IteraThor/IT2-Documentation/images/05_baseplate/01_front_back.png

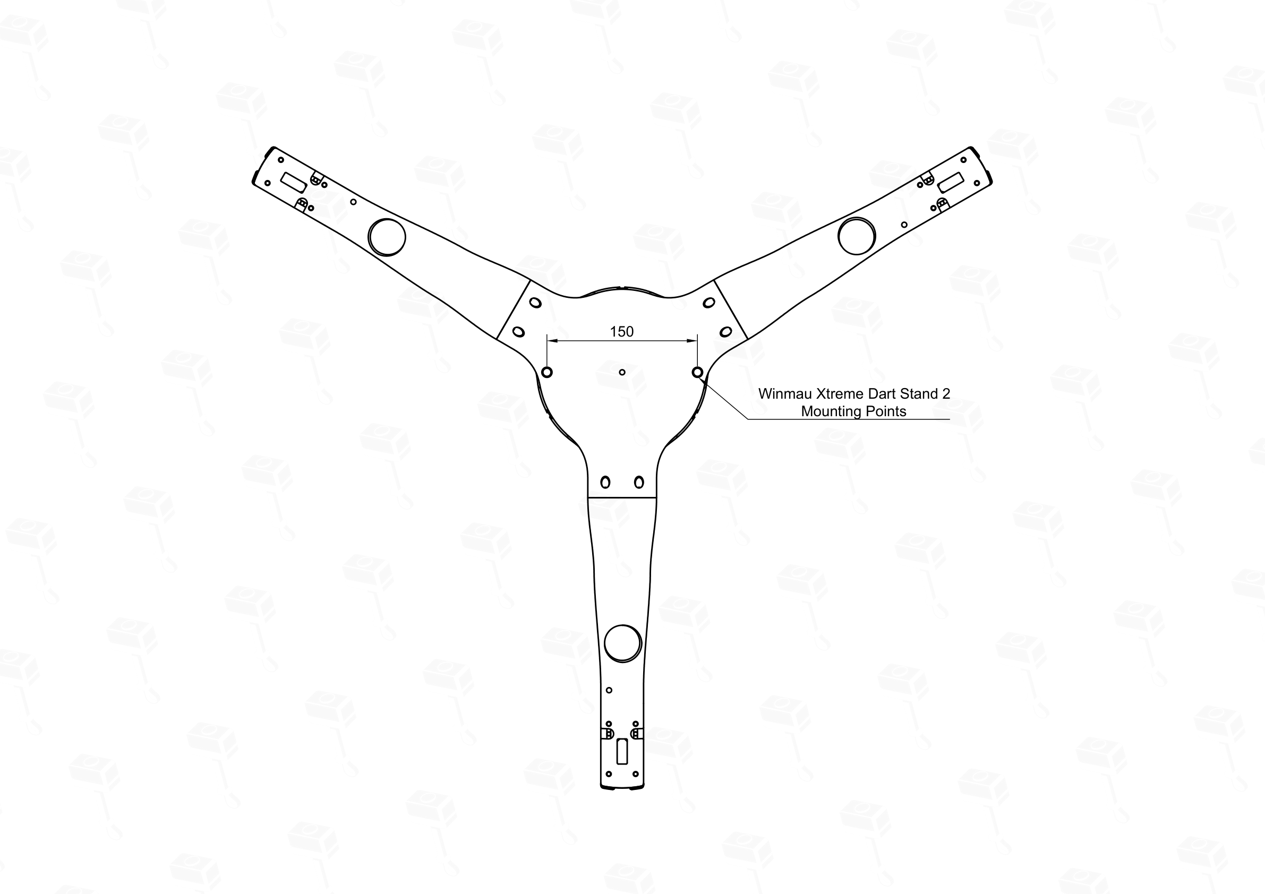
images/05_baseplate/01_front_back.png
