IteraThor/IT2-Documentation/images/05_baseplate/03_front_view.png

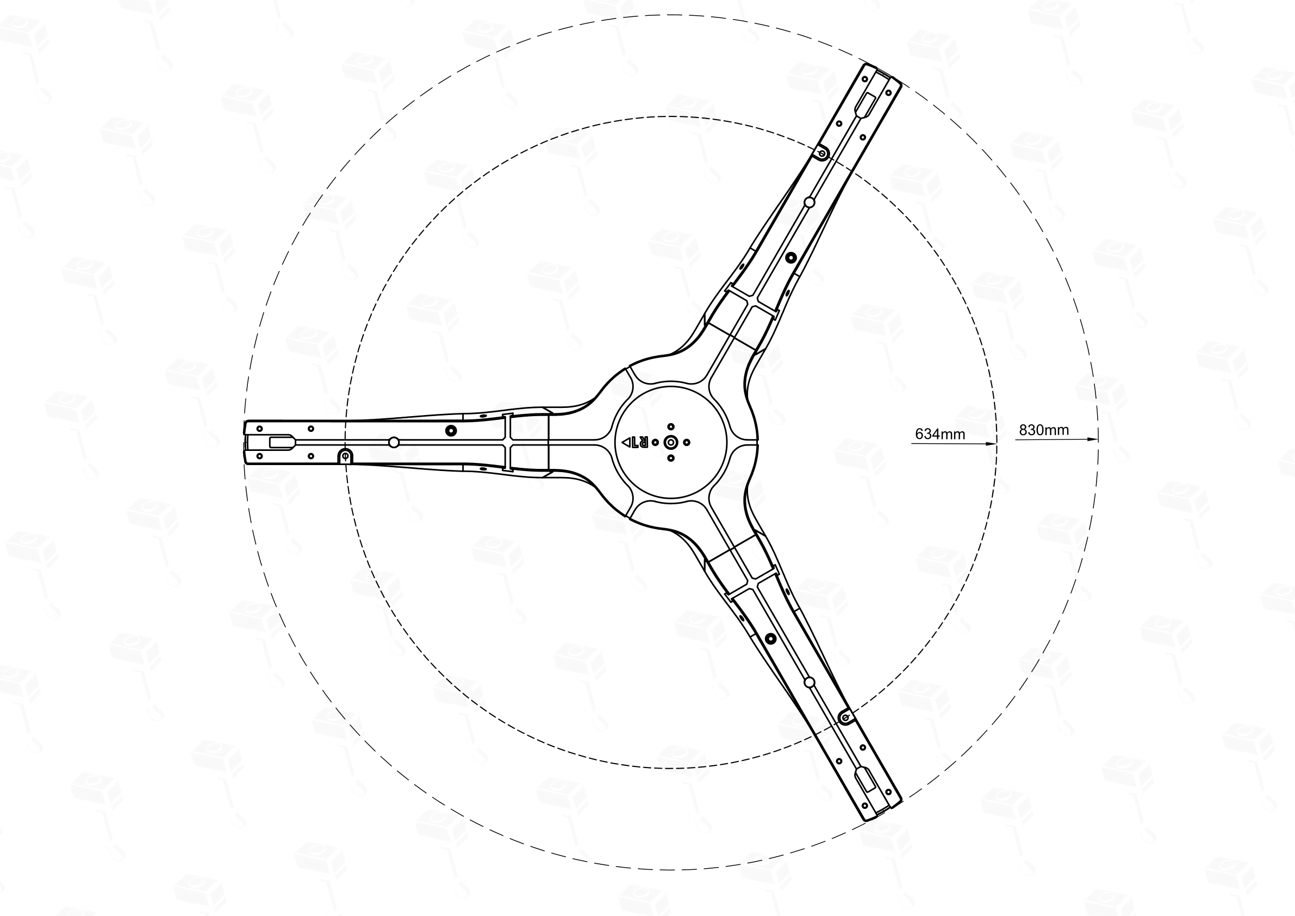
images/05_baseplate/03_front_view.png
