IteraThor/IT2-Documentation/images/inserted-heat-insert.png

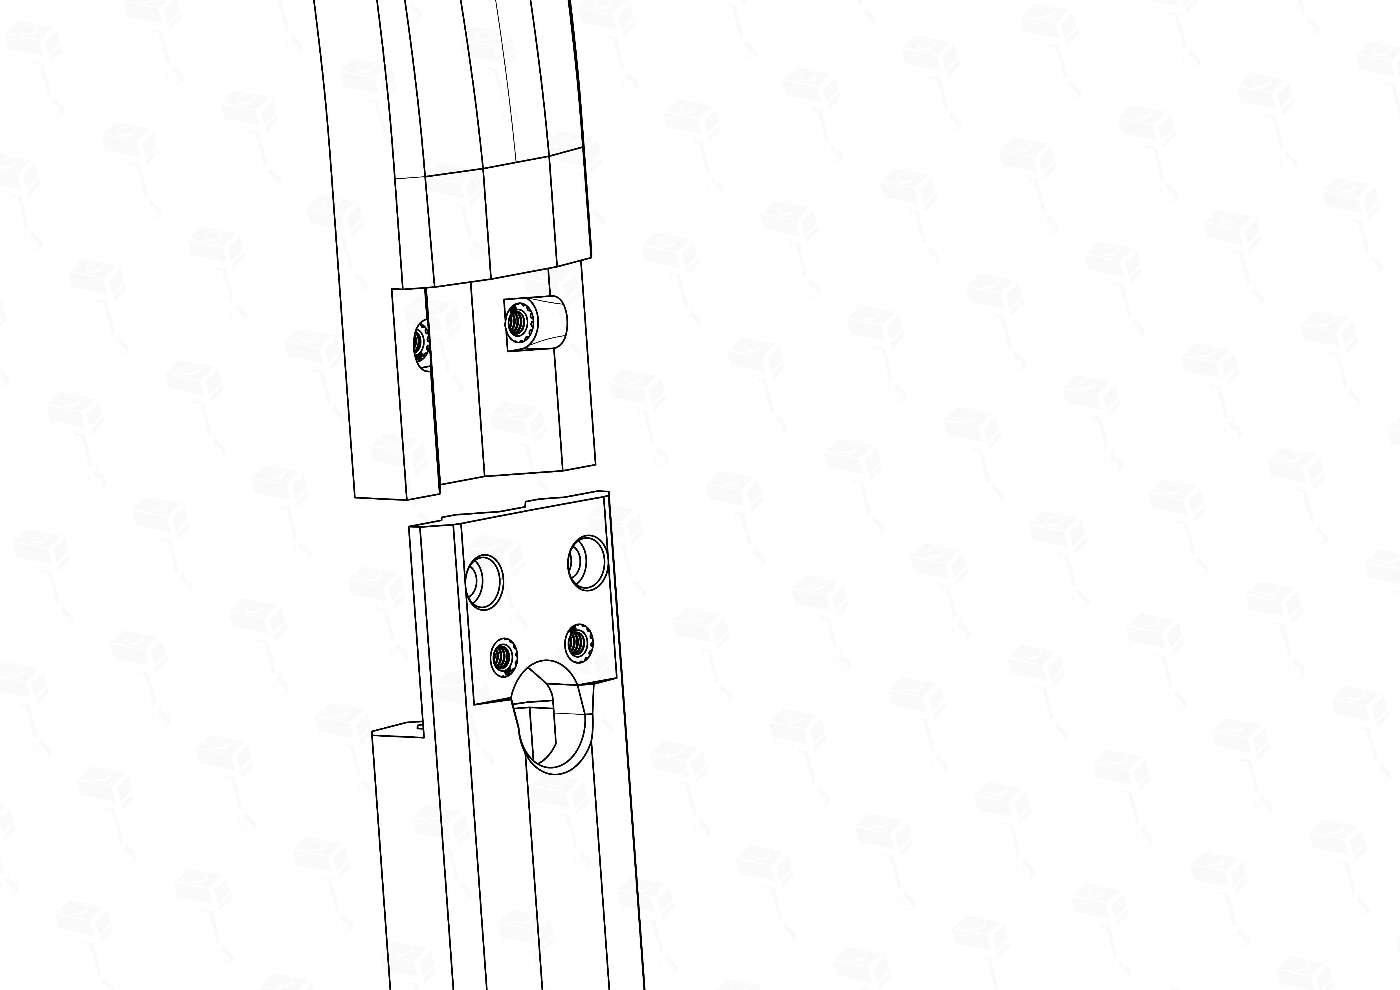
images/inserted-heat-insert.png
