IteraThor/IT2-Documentation/images/usb-camera-cable.png

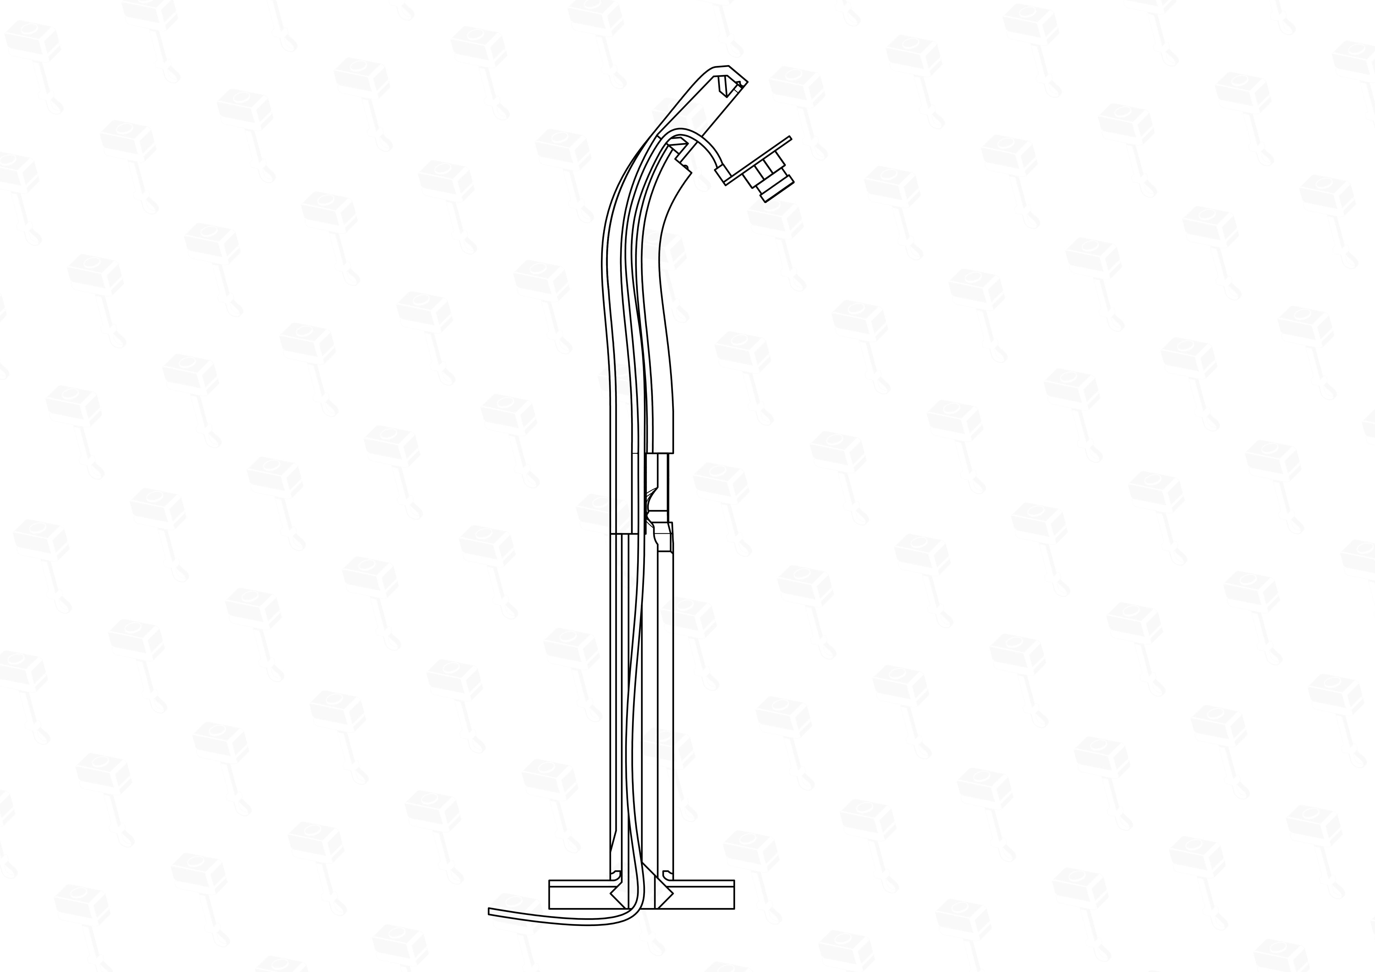
images/usb-camera-cable.png
